mateuszkojro/hapmd/src/rotor/rotor-shaft/include/A4988.h

#include "Arduino.h"
class A4988
{
public:
// if pin is disabled
#define DISABLED_PIN UINT8_MAX

    enum Direction
    {
        CW = HIGH,
        CCW = LOW
    };

    A4988(const uint8_t step_pin, const uint8_t dir_pin) : step_pin(step_pin),
                                                           dir_pin(dir_pin)
    {
        /*
        In simple configuration, driver is always enabled, never sleeps, does not require any step division
        thus only two pins that need to be addressed are step and dir pin.
        The rest of addressable pins will be disabled
        */
        pinMode(step_pin, OUTPUT);
        pinMode(dir_pin, OUTPUT);
        digitalWrite(dir_pin, Direction::CW);
    }

    /**
     * @brief checks weather pin is disabled or not
     *
     * @param pin to check
     * @return true if in is disabled
     * @return false if is enabled
     */
    bool IsDisabled(const uint8_t pin)
    {
        return (pin == DISABLED_PIN);
    }

    /**
     * @brief move motor's shaft
     *
     * @param no_steps no steps to move, default: 1
     */
    void Step(int no_steps = 1)
    {
        for (int i = 0; i < no_steps; i++)
        {
            digitalWrite(step_pin, HIGH);
            delayMicroseconds(1000);
            digitalWrite(step_pin, LOW);
            delayMicroseconds(1000);
        }
    }

    /**
     * @brief Set the rotation direction
     *
     * @param direction new rotation direction
     */
    void SetDirection(const Direction direction)
    {
        digitalWrite(dir_pin, direction);
    }

protected:
    // Stepper Motor Driver
    // main driver control pins
    uint8_t step_pin;
    uint8_t dir_pin;

    // general utility
    uint8_t enable_pin = DISABLED_PIN;
    uint8_t sleep_pin = DISABLED_PIN;
    uint8_t reset_pin = DISABLED_PIN;

    // step division pins
    uint8_t ms1_pin = DISABLED_PIN;
    uint8_t ms2_pin = DISABLED_PIN;
    uint8_t ms3_pin = DISABLED_PIN;
};
